attssystem/laser_game/LIR_prgm/src/sound.h

// Sound Requirements

char notes[] = "gabygabyxzCDxzCDabywabywzCDEzCDEbywFCDEqywFGDEqi        azbC"; // a space represents a rest
int length = sizeof(notes); // the number of notes
 int beats[] = { 1, 1, 1, 1, 1, 1, 1, 1, 1, 1, 1, 1, 1, 1, 1, 1, 1, 1, 1, 1, 1, 1, 1, 1, 1, 1, 1, 1, 1, 1, 1, 1, 1, 1, 1, 1, 1, 1, 1, 1, 1, 1, 1, 1, 1, 1, 1, 1, 1, 1, 1, 1, 1, 1, 1, 1, 2, 3, 3, 16,};
int tempo = 75;

void playTone(int tone, int delayTime) {
  for (long i = 0; i < delayTime * 1000L; i += tone * 2) {
    digitalWrite(speakerPin, HIGH);
    delayMicroseconds(tone);
    digitalWrite(speakerPin, LOW);
    delayMicroseconds(tone);
  }
}

void playNote(char note, int delayTime) {
  char names[] = { 'c', 'd', 'e', 'f', 'g', 'x', 'a', 'z', 'b', 'C', 'y', 'D', 'w', 'E', 'F', 'q', 'G', 'i' };
  // c=C4, C = C5. These values have been tuned.
  int tones[] = { 1898, 1690, 1500, 1420, 1265, 1194, 1126, 1063, 1001, 947, 893, 843, 795, 749, 710, 668, 630, 594 };

  // play the tone corresponding to the note name
  for (int i = 0; i < 18; i++) {
    if (names[i] == note) {
      playTone(tones[i], delayTime);
    }
  }
}

void soundFX(float amplitude, float period) {
  int delayTime = 2 + amplitude + amplitude * sin(millis() / period);
  for (int i = 0; i < 5; i++) {
    digitalWrite(speakerPin, HIGH);
    delayMicroseconds(delayTime);
    digitalWrite(speakerPin, LOW);
    delayMicroseconds(delayTime);
  }
}
